X-Lemon-X/Pilot_6_axis/pilot_frimware/src/OledPrintLib.h

#pragma once
// #include <string>

#include <Adafruit_GFX.h>
#include <Adafruit_SSD1306.h>
#include <vector>


class OledPrintLib {
private:
  Adafruit_SSD1306 *screen = NULL;
  std::vector<String> bufforStrings;

  int lineCount              = 0;
  int endLineIndex           = 0;
  int charactersMaxContWidth = 0;

  void DislpayPrint();

public:
  OledPrintLib(Adafruit_SSD1306 *screen, int lineCount, int charactersMaxContWidth);
  ~OledPrintLib() {
  }
  void UpdateLine(String string, int line);
  void UpdateLine(String string);
  void Print(String string);
  void Println(String string);
};
